jprojektde/Arduino-Clock-Projector/Arduino/demo/mappings.cpp

/*
 * mappings.cpp
 *
 *  Created on: Dec 29, 2023
 *      Author: jakob
 */


#include "Projektor.h"


uint8_t Projektor_mapping[23] = {76,56,57,65,73,72,77,	8,16,17,8,1,0,9,	32,40,41,49,25,24,33,	64,		48};

uint8_t Projektor_Buffer[9];

uint8_t Seven_SegmentASCII[96] = {
	0x00, /* (space) */
	0x86, /* ! */
	0x22, /* " */
	0x7E, /* # */
	0x6D, /* $ */
	0xD2, /* % */
	0x46, /* & */
	0x20, /* ' */
	0x29, /* ( */
	0x0B, /* ) */
	0x21, /* * */
	0x70, /* + */
	0x10, /* , */
	0x40, /* - */
	0x80, /* . */
	0x52, /* / */
	0x3F, /* 0 */
	0x06, /* 1 */
	0x5B, /* 2 */
	0x4F, /* 3 */
	0x66, /* 4 */
	0x6D, /* 5 */
	0x7D, /* 6 */
	0x07, /* 7 */
	0x7F, /* 8 */
	0x6F, /* 9 */
	0x09, /* : */
	0x0D, /* ; */
	0x61, /* < */
	0x48, /* = */
	0x43, /* > */
	0xD3, /* ? */
	0x5F, /* @ */
	0x77, /* A */
	0x7C, /* B */
	0x39, /* C */
	0x5E, /* D */
	0x79, /* E */
	0x71, /* F */
	0x3D, /* G */
	0x76, /* H */
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
	0x00, /* (del) */
};
